prodellkin/Projects/Riga 104/УКВ-1-1с на TA7358 v1.0.pdf

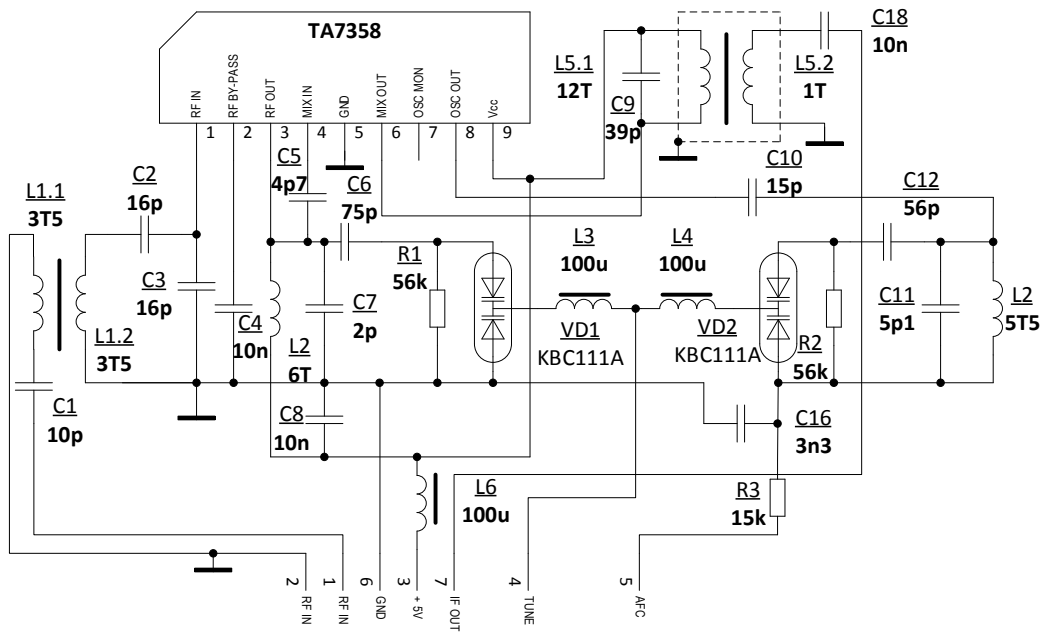
[picture p31: page 1]
